PiKeeb/30cent-keyboard/case_files/MiddleUSB.step

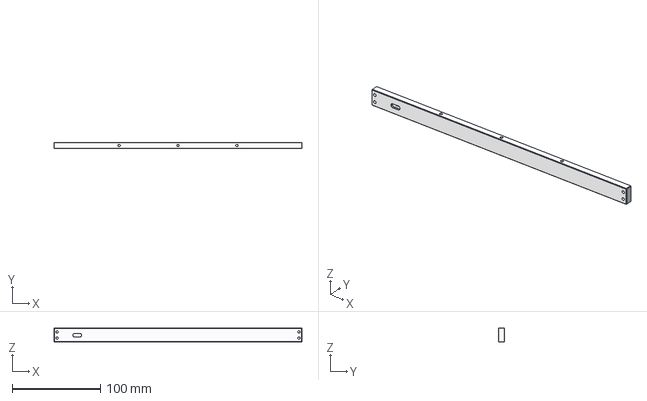
[picture p15: CAD file, 2023-07-02]
case_files/MiddleUSB.step
281.1 x 7.00 x 16.0 mm
