PiKeeb/30cent-keyboard/case_files/MiddleTopSide.step

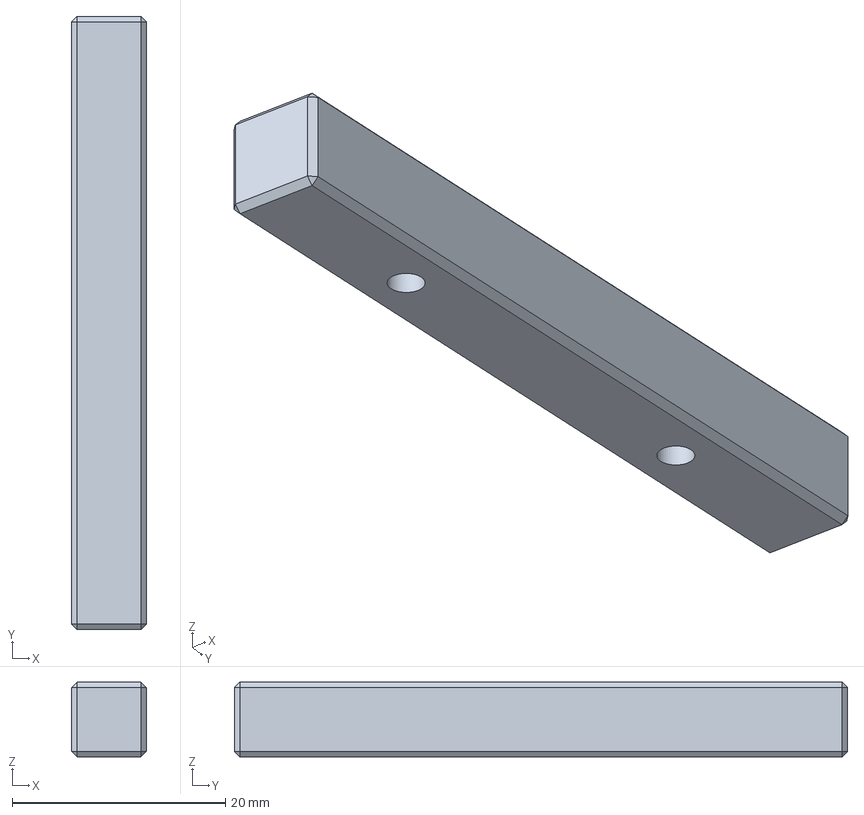
[picture p16: CAD file, 2023-07-02]
case_files/MiddleTopSide.step
7.00 x 57.5 x 7.00 mm
