PiKeeb/30cent-keyboard/pcb_files/kicad_project/30cent.kicad_sch

## KiCad design pcb_files/kicad_project/30cent.kicad_sch (2023-07-02)

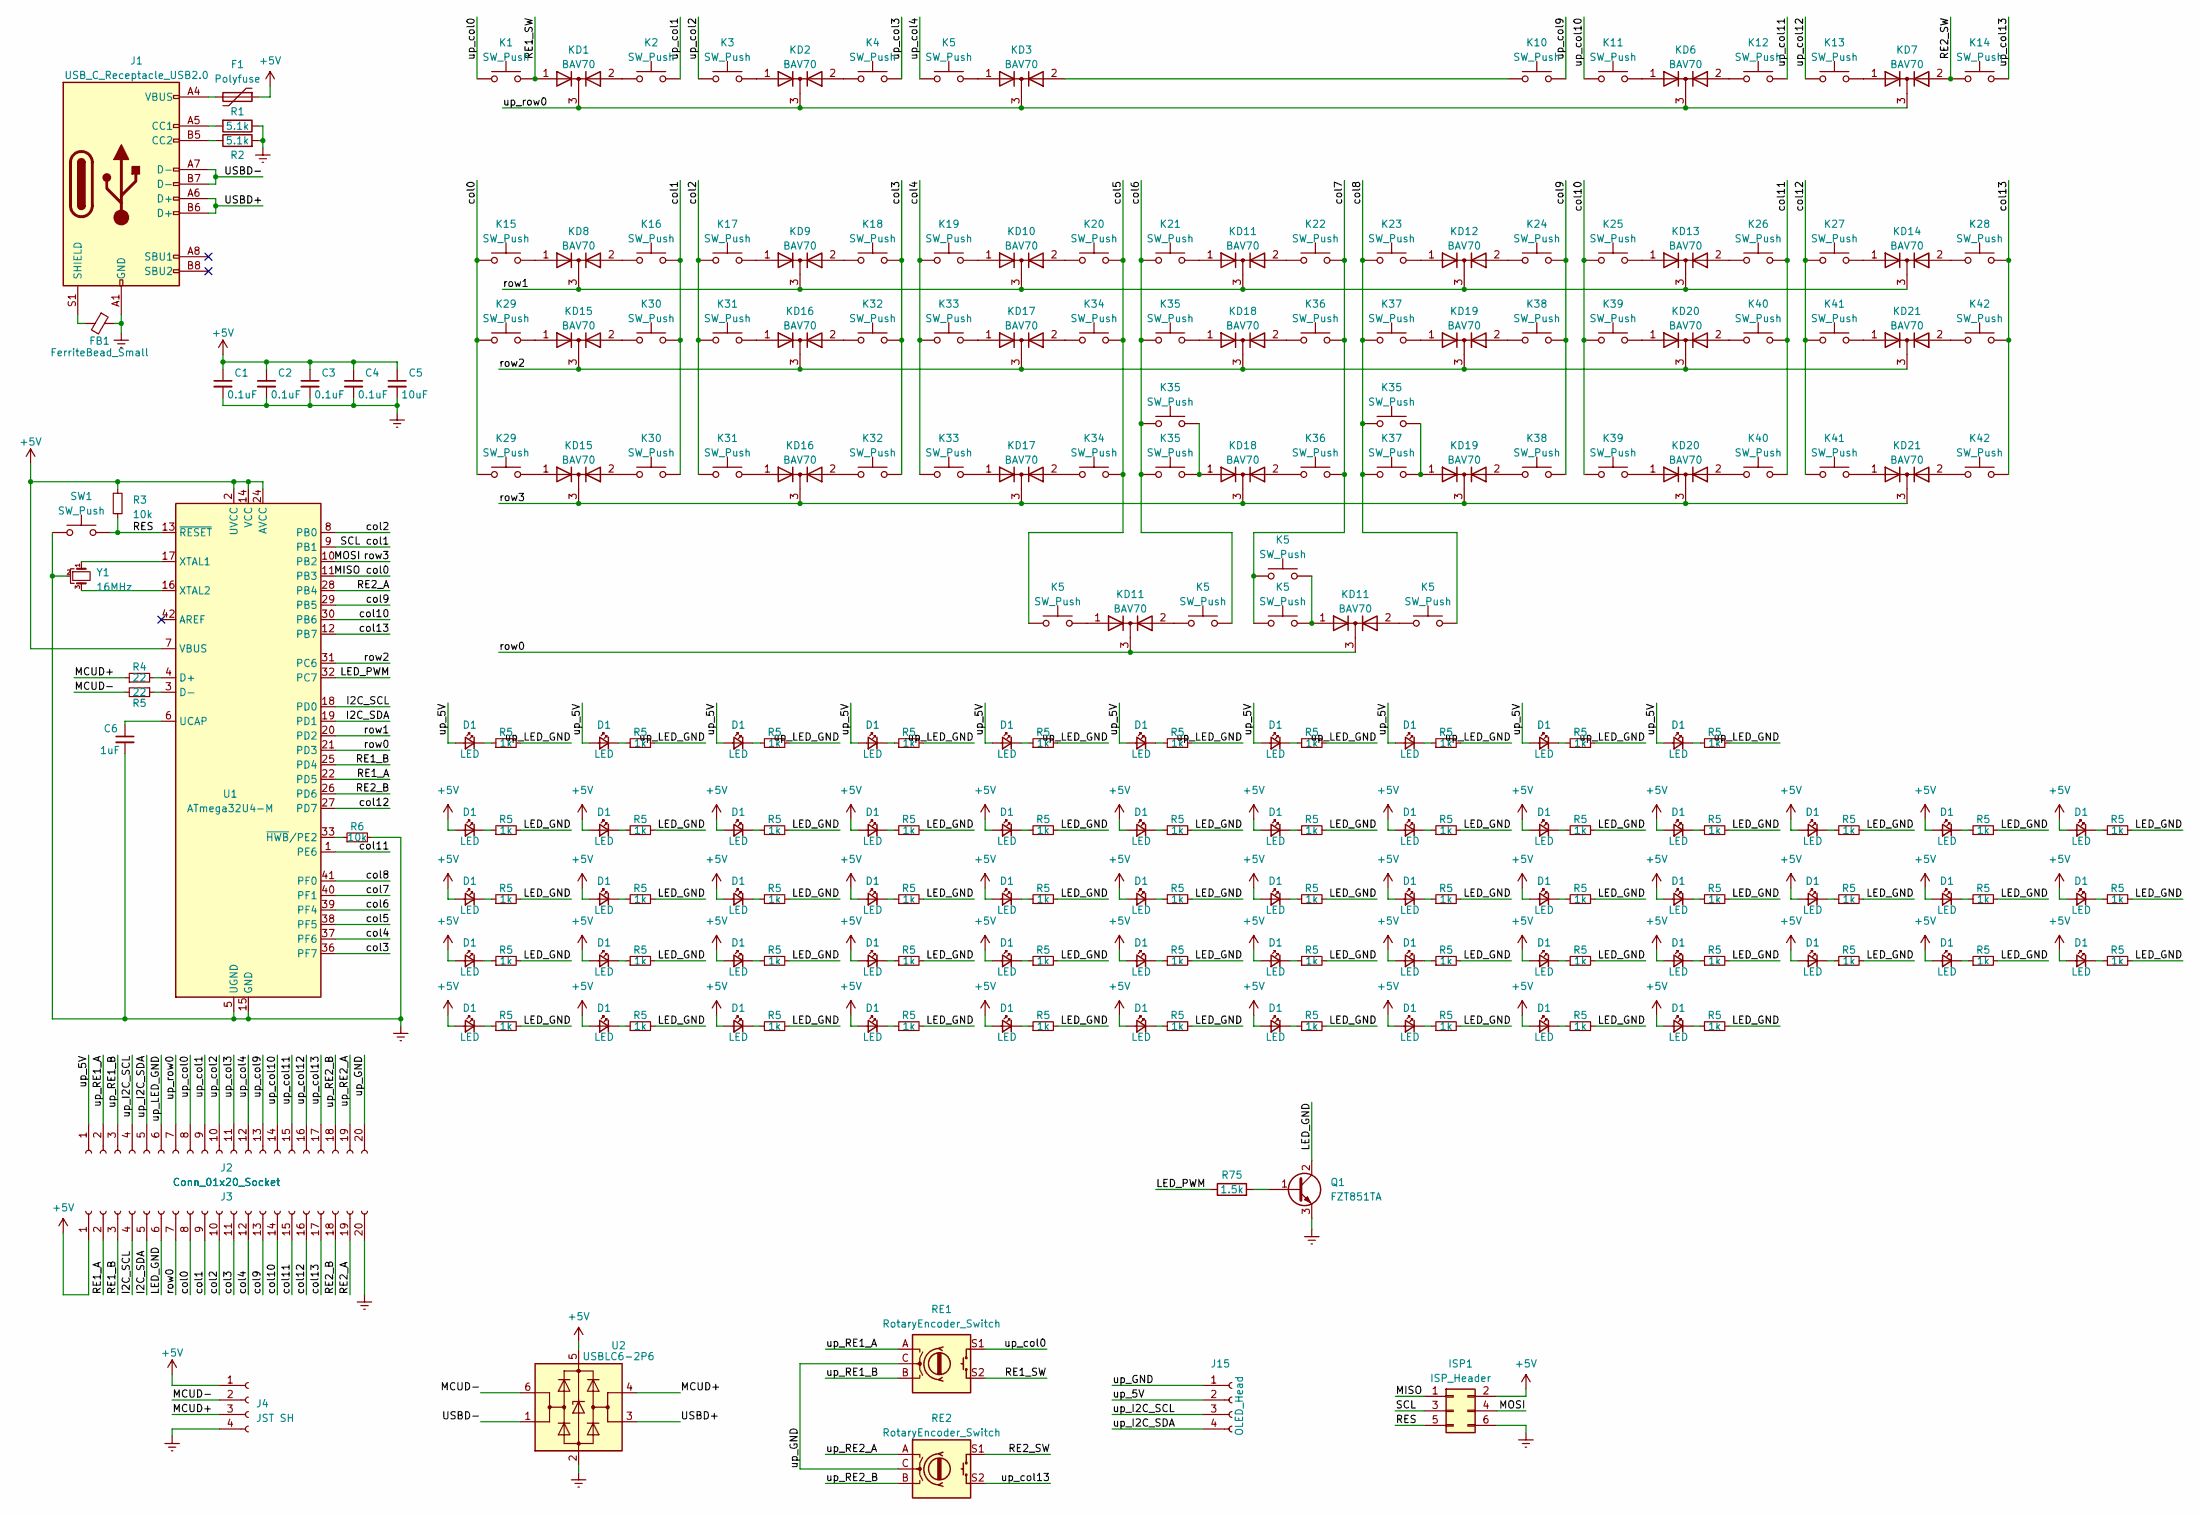
[picture p17: schematic 30cent.kicad_sch]

Parts:
C1, C2, C3, C4: 0.1uF; C_0402_1005Metric
C5: 10uF; C_0402_1005Metric
C6: 1uF; C_0402_1005Metric
D1: LED; MX_LED_1.8mm
F1: Polyfuse; Fuse_0805_2012Metric
FB1: FerriteBead_Small; L_0805_2012Metric
ISP1: ISP_Header; PinHeader_2x03_P2.54mm_Vertical
J1: USB_C_Receptacle_USB2.0; USB_C_Receptacle_HRO_TYPE-C-31-M-12
J2, J3: Conn_01x20_Socket; Omron_XF2M-2015-1A_1x20-1MP_P0.5mm_Horizontal
J4: JST SH; JST_SH_SM04B-SRSS-TB_1x04-1MP_P1.00mm_Horizontal
J15: OLED_Head; Screen_SSD1306_0.91inch
K1, K2, K3, K4, K5, K10, K11, K12, K13, K14, K15, K16, K17, K18, K19, K20, K21, K22, K23, K24, K25, K26, K27, K28, K29, K30, K31, K32, K33, K34, K35, K36, K37, K38, K39, K40, K41, K42: SW_Push; MX_Kailhua_Socket_1.00u_HoledPads
KD1, KD2, KD3, KD6, KD7, KD8, KD9, KD10, KD11, KD12, KD13, KD14, KD15, KD16, KD17, KD18, KD19, KD20, KD21: BAV70; SOT-23
Q1: FZT851TA; SOT-223-3_TabPin2
R1, R2: 5.1k; R_0402_1005Metric
R3, R6: 10k; R_0402_1005Metric
R4: 22; R_0402_1005Metric
R5: 1k; R_0603_1608Metric
R75: 1.5k; R_0603_1608Metric
RE1, RE2: RotaryEncoder_Switch
SW1: SW_Push; SW_SPST_TL3342
U1: ATmega32U4-M; QFN-44-1EP_7x7mm_P0.5mm_EP5.2x5.2mm
U2: USBLC6-2P6; SOT-666
Y1: 16MHz; Resonator_SMD_Murata_CSTxExxV-3Pin_3.0x1.1mm

Connections:
+5V: C1.1, C2.1, C3.1, C4.1, C5.1, D1.2 (A), F1.1, ISP1.2, J3.1, J4.1, R3.1, U1.2 (UVCC), U1.7 (VBUS), U1.14 (VCC), U1.24 (AVCC), U1.34 (VCC), U1.44 (AVCC), U2.5 (VBUS)
Earth: C1.2, C2.2, C3.2, C4.2, C5.2, C6.2, FB1.1, ISP1.6, J1.A1 (GND), J1.A12 (GND), J1.B1 (GND), J1.B12 (GND), J3.20, J4.4, Q1.3 (E), R1.1, R2.2, R6.2, SW1.1, U1.5 (UGND), U1.15 (GND), U1.23 (GND), U1.35 (GND), U1.43 (GND), U1.45 (GND), U2.2 (GND), Y1.2
I2C_SCL: J3.4, U1.18 (PD0)
I2C_SDA: J3.5, U1.19 (PD1)
LED_GND: J3.6, Q1.2 (C), R5.2
LED_PWM: R75.1, U1.32 (PC7)
MCUD+: J4.3, R4.1, U2.4 (I/O2)
MCUD-: J4.2, R5.2, U2.6 (I/O1)
MOSI: ISP1.4, KD15.3 (K), KD16.3 (K), KD17.3 (K), KD18.3 (K), KD19.3 (K), KD20.3 (K), KD21.3 (K), U1.10 (PB2)
unnamed: C6.1, U1.6 (UCAP)
unnamed: D1.1 (K), R5.1
unnamed: F1.2, J1.A4 (VBUS), J1.A9 (VBUS), J1.B4 (VBUS), J1.B9 (VBUS)
unnamed: FB1.2, J1.S1 (SHIELD)
unnamed: J1.A5 (CC1), R1.2
unnamed: J1.B5 (CC2), R2.1
unnamed: K2.2, KD1.2 (A)
unnamed: K3.1, KD2.1 (A)
unnamed: K4.2, KD2.2 (A)
unnamed: K5.1, KD3.1 (A), KD11.2 (A)
unnamed: K5.2, KD11.1 (A)
unnamed: K10.2, KD3.2 (A)
unnamed: K11.1, KD6.1 (A)
unnamed: K12.2, KD6.2 (A)
unnamed: K13.1, KD7.1 (A)
unnamed: K15.1, KD8.1 (A)
unnamed: K16.2, KD8.2 (A)
unnamed: K17.1, KD9.1 (A)
unnamed: K18.2, KD9.2 (A)
unnamed: K19.1, KD10.1 (A)
unnamed: K20.2, KD10.2 (A)
unnamed: K21.1, KD11.1 (A)
unnamed: K22.2, KD11.2 (A)
unnamed: K23.1, KD12.1 (A)
unnamed: K24.2, KD12.2 (A)
unnamed: K25.1, KD13.1 (A)
unnamed: K26.2, KD13.2 (A)
unnamed: K27.1, KD14.1 (A)
unnamed: K28.2, KD14.2 (A)
unnamed: K29.1, KD15.1 (A)
unnamed: K30.2, KD15.2 (A)
unnamed: K31.1, KD16.1 (A)
unnamed: K32.2, KD16.2 (A)
unnamed: K33.1, KD17.1 (A)
unnamed: K34.1, KD17.2 (A)
unnamed: K34.2, KD17.2 (A)
unnamed: K35.1, K35.2, KD18.1 (A)
unnamed: K35.2, K37.1, KD19.1 (A)
unnamed: K36.1, KD18.2 (A)
unnamed: K36.2, KD18.2 (A)
unnamed: K37.1, KD19.1 (A)
unnamed: K38.2, KD19.2 (A)
unnamed: K39.1, KD20.1 (A)
unnamed: K40.2, KD20.2 (A)
unnamed: K41.1, KD21.1 (A)
unnamed: K42.2, KD21.2 (A)
unnamed: Q1.1 (B), R75.2
unnamed: R4.2, U1.4 (D+)
unnamed: R5.1, U1.3 (D-)
unnamed: R6.1, U1.33 (~HWB/PE2)
unnamed: U1.16 (XTAL2), Y1.3
unnamed: U1.17 (XTAL1), Y1.1
RE1_A: J3.2, U1.22 (PD5)
RE1_B: J3.3, U1.25 (PD4)
RE1_SW: K1.1, KD1.1 (A), RE1.S2
RE2_A: J3.19, U1.28 (PB4)
RE2_B: J3.18, U1.26 (PD6)
RE2_SW: K14.2, KD7.2 (A), RE2.S1
RES: ISP1.5, R3.2, SW1.2, U1.13 (~RESET)
USBD+: J1.A6 (D+), J1.B6 (D+), U2.3 (I/O2)
USBD-: J1.A7 (D-), J1.B7 (D-), U2.1 (I/O1)
col0: ISP1.1, J3.8, K15.2, K29.2, U1.11 (PB3)
col1: ISP1.3, J3.9, K16.1, K30.1, U1.9 (PB1)
col2: J3.10, K17.2, K31.2, U1.8 (PB0)
col3: J3.11, K18.1, K32.1, U1.36 (PF7)
col4: J3.12, K19.2, K33.2, U1.37 (PF6)
col5: K5.1, K20.1, K34.1, K34.2, U1.38 (PF5)
col6: K5.2, K21.2, K35.1, K35.2, U1.39 (PF4)
col7: K5.1, K22.1, K36.1, K36.2, U1.40 (PF1)
col8: K5.2, K23.2, K35.1, K37.2, U1.41 (PF0)
col9: J3.13, K24.1, K38.1, U1.29 (PB5)
col10: J3.14, K25.2, K39.2, U1.30 (PB6)
col11: J3.15, K26.1, K40.1, U1.1 (PE6)
col12: J3.16, K27.2, K41.2, U1.27 (PD7)
col13: J3.17, K28.1, K42.1, U1.12 (PB7)
row0: J3.7, KD11.3 (K), U1.21 (PD3)
row1: KD8.3 (K), KD9.3 (K), KD10.3 (K), KD11.3 (K), KD12.3 (K), KD13.3 (K), KD14.3 (K), U1.20 (PD2)
row2: KD15.3 (K), KD16.3 (K), KD17.3 (K), KD18.3 (K), KD19.3 (K), KD20.3 (K), KD21.3 (K), U1.31 (PC6)
up_5V: D1.2 (A), J2.1, J15.2
up_GND: J2.20, J15.1, RE1.C, RE2.C
up_I2C_SCL: J2.4, J15.3
up_I2C_SDA: J2.5, J15.4
up_LED_GND: J2.6, R5.2
up_RE1_A: J2.2, RE1.A
up_RE1_B: J2.3, RE1.B
up_RE2_A: J2.19, RE2.A
up_RE2_B: J2.18, RE2.B
up_col0: J2.8, K1.2, RE1.S1
up_col1: J2.9, K2.1
up_col2: J2.10, K3.2
up_col3: J2.11, K4.1
up_col4: J2.12, K5.2
up_col9: J2.13, K10.1
up_col10: J2.14, K11.2
up_col11: J2.15, K12.1
up_col12: J2.16, K13.2
up_col13: J2.17, K14.1, RE2.S2
up_row0: J2.7, KD1.3 (K), KD2.3 (K), KD3.3 (K), KD6.3 (K), KD7.3 (K)
